ronnypoto/cosite-interference-canceller/A_Schematic/Schematic.kicad_sch

## KiCad design A_Schematic/Schematic.kicad_sch (2026-09-05)

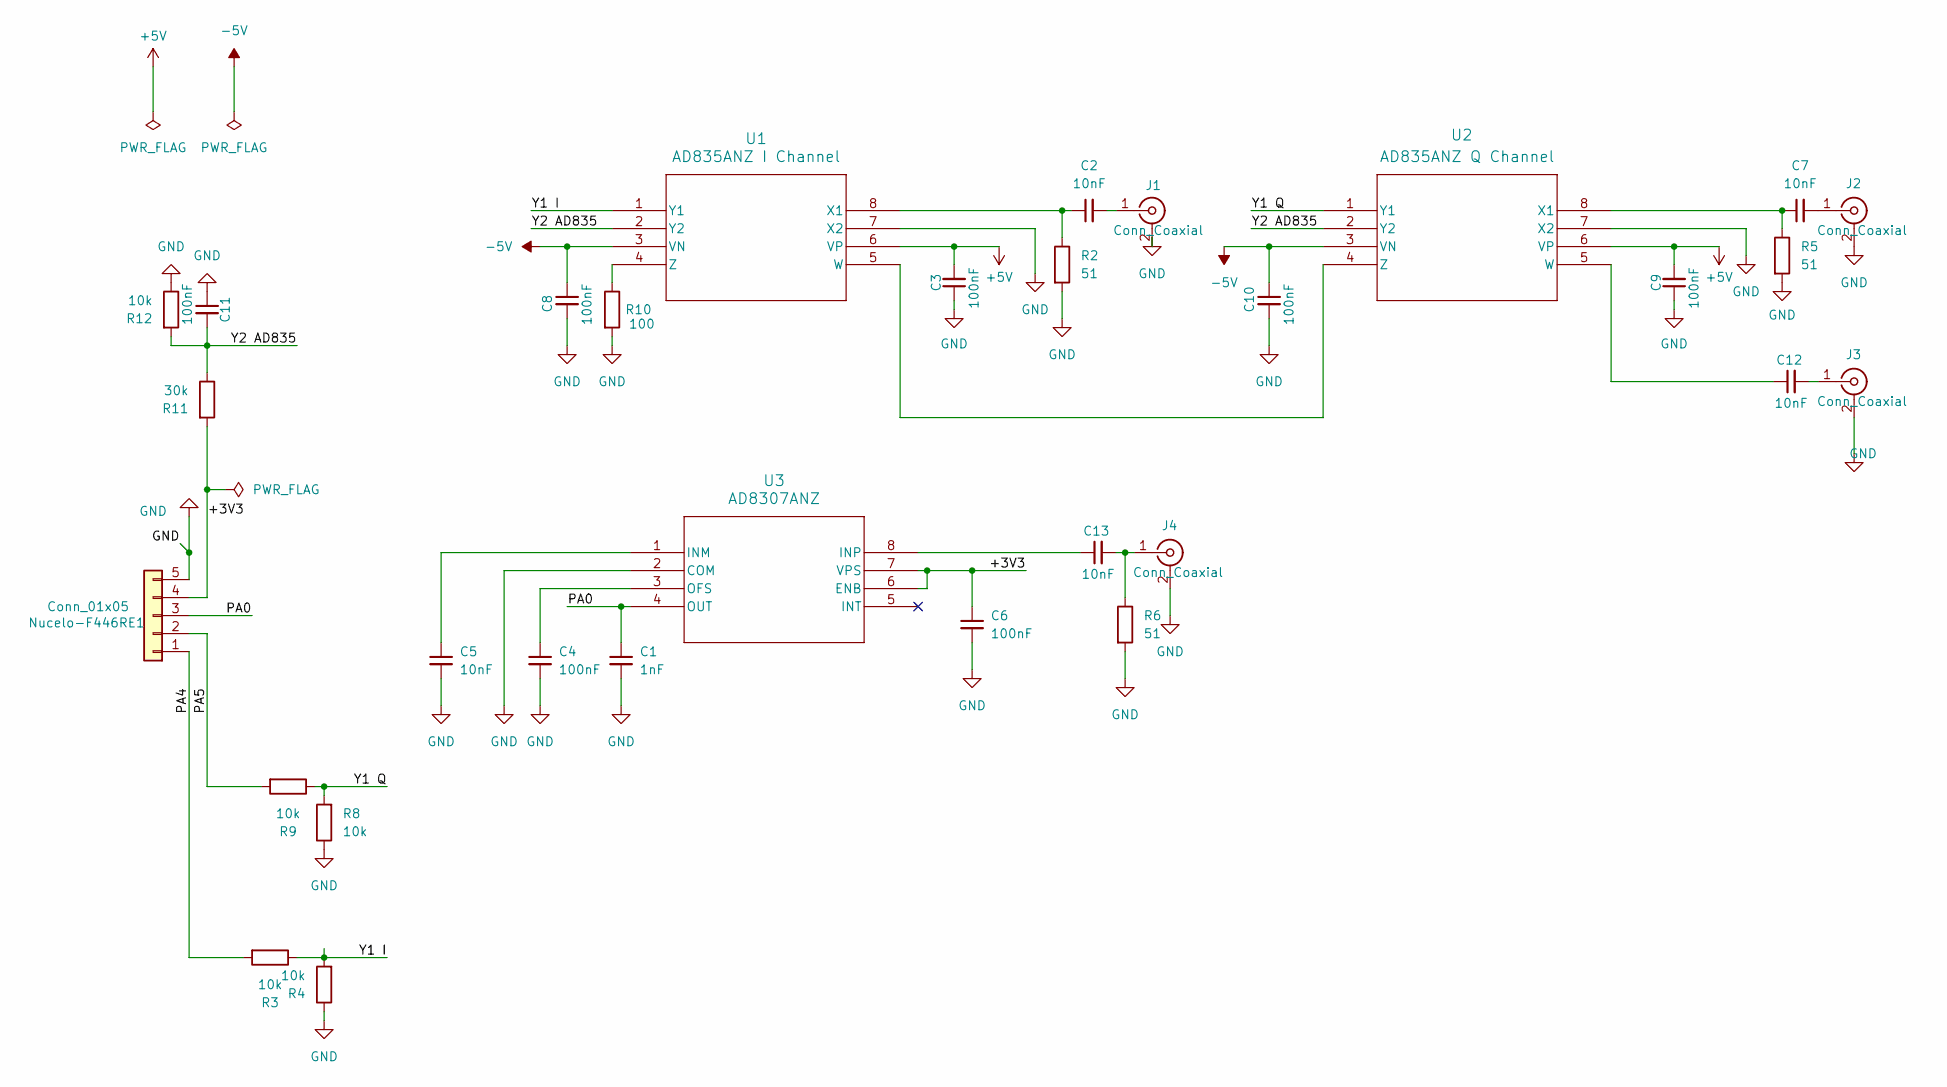
[picture p8: schematic Schematic.kicad_sch]

Parts:
C1: 1nF
C2, C5, C7, C12, C13: 10nF
C3, C4, C6, C8, C9, C10, C11: 100nF
J1, J2, J3, J4: Conn_Coaxial
Nucelo-F446RE1: Conn_01x05
R2, R5, R6: 51
R3, R4, R8, R9, R12: 10k
R10: 100
R11: 30k
U1: AD835ANZ I Channel; N_8_ADI
U2: AD835ANZ Q Channel; N_8_ADI
U3: AD8307ANZ; N_8_ADI

Connections:
+3V3: C6.1, Nucelo-F446RE1.4, R11.2, U3.6 (ENB), U3.7 (VPS)
+5V: C3.2, C9.2, U1.6 (VP), U2.6 (VP)
-5V: C8.1, C10.1, U1.3 (VN), U2.3 (VN)
GND: C1.2, C3.1, C4.2, C5.2, C6.2, C8.2, C9.1, C10.2, C11.1, J1.2 (Ext), J2.2 (Ext), J3.2 (Ext), J4.2 (Ext), Nucelo-F446RE1.5, R2.2, R4.1, R5.2, R6.2, R8.1, R10.2, R12.1, U1.7 (X2), U2.7 (X2), U3.2 (COM)
unnamed: C2.1, R2.1, U1.8 (X1)
unnamed: C2.2, J1.1 (In)
unnamed: C4.1, U3.3 (OFS)
unnamed: C5.1, U3.1 (INM)
unnamed: C7.1, R5.1, U2.8 (X1)
unnamed: C7.2, J2.1 (In)
unnamed: C12.1, U2.5 (W)
unnamed: C12.2, J3.1 (In)
unnamed: C13.1, U3.8 (INP)
unnamed: C13.2, J4.1 (In), R6.1
unnamed: R10.1, U1.4 (Z)
unnamed: U1.5 (W), U2.4 (Z)
PA0: C1.1, Nucelo-F446RE1.3, U3.4 (OUT)
PA4: Nucelo-F446RE1.1, R3.2
PA5: Nucelo-F446RE1.2, R9.2
Y1 I: R3.1, R4.2, U1.1 (Y1)
Y1 Q: R8.2, R9.1, U2.1 (Y1)
Y2 AD835: C11.2, R11.1, R12.2, U1.2 (Y2), U2.2 (Y2)
